martinberlin/Sharp-LV/components/3D/LCD-10S-0.5SH.step

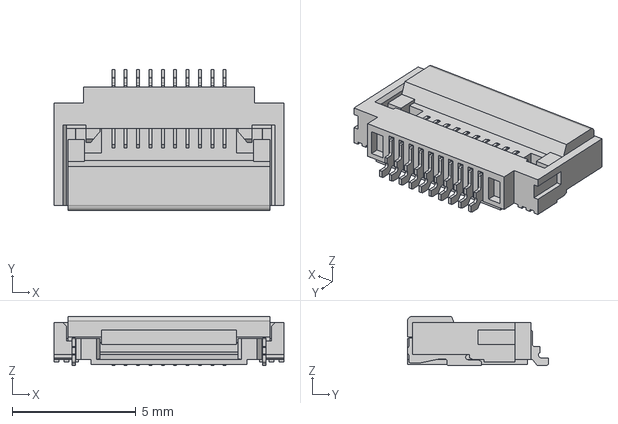
[picture p17: CAD file, 2024-05-29]
components/3D/LCD-10S-0.5SH.step
9.30 x 5.70 x 2.00 mm
