martinberlin/Sharp-LV/components/3D/MOLEX_502426-0810.stp

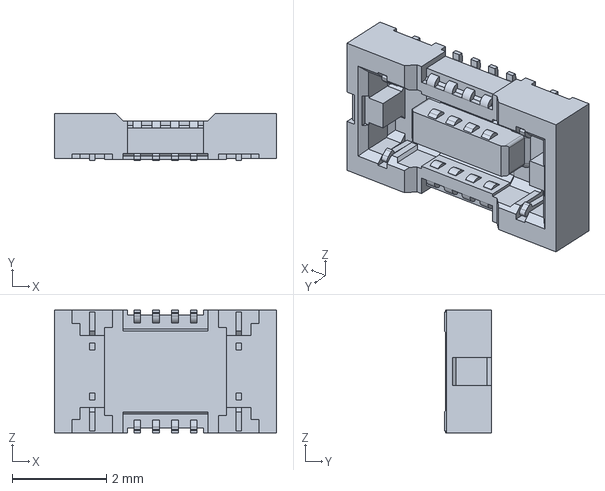
[picture p18: CAD file, 2024-05-29]
components/3D/MOLEX_502426-0810.stp
4.70 x 1.00 x 2.60 mm
