martinberlin/Sharp-LV/components/3D/NRF52840-QIAA-R.stp

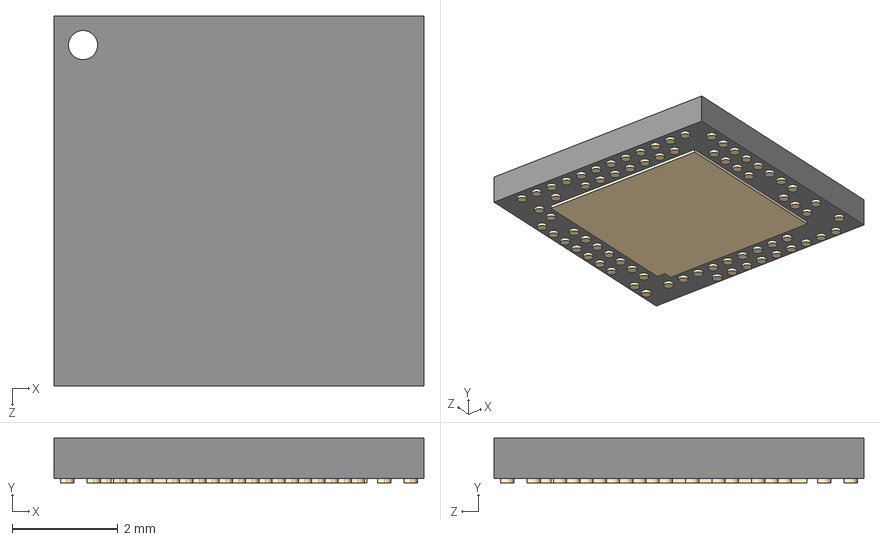
[picture p19: CAD file, 2024-05-29]
components/3D/NRF52840-QIAA-R.stp
7.00 x 0.85 x 7.00 mm
